solemnify2/REDKITE-F16-Panels/F16_LEFT_AUX_MISC/BiosHandler/DcsBiosParser.h

/*
  DcsBiosParser.h — DCS-BIOS binary frame parser for Teensy

  DCS-BIOS protocol:
    Sync: 0x55 0x55 0x55 0x55
    Then repeating: ADDR_LOW ADDR_HIGH COUNT_LOW COUNT_HIGH DATA[count]
    Frame end marker: address=0x5555, count=0x5555

  Only output addresses (LED control) are handled here.
  Switch input is handled via USB joystick (no DCS-BIOS write needed).
*/

#ifndef DCSBIOS_PARSER_H
#define DCSBIOS_PARSER_H

// ================================================================
//  DCS-BIOS F-16C Address Map
// ================================================================
// Source: DCS-BIOS F-16C_50.json
// These addresses may need verification against the actual JSON export.

// Address 0x447A: Nose gear (bit14), Left gear (bit15)
#define DCSBIOS_GEAR_NL_ADDR    0x447A
#define DCSBIOS_GEAR_NOSE_MASK  0x4000  // bit 14
#define DCSBIOS_GEAR_LEFT_MASK  0x8000  // bit 15

// Address 0x447C: Right gear (bit0)
#define DCSBIOS_GEAR_R_ADDR     0x447C
#define DCSBIOS_GEAR_RIGHT_MASK 0x0001  // bit 0

// Address 0x447C: Right gear (bit0), Gear Warning (bit1)
#define DCSBIOS_GEAR_WARN_MASK  0x0002  // bit 1 — LIGHT_GEAR_WARN (red)

// Address 0x447E: RWR/TWA + ADV indicator lights
#define DCSBIOS_TWA_ADDR          0x447E
#define DCSBIOS_ADV_ACTIVE_MASK   0x0004  // bit 2  — LIGHT_ACTIVE (green)
#define DCSBIOS_ADV_STBY_MASK     0x0008  // bit 3  — LIGHT_STBY (yellow)
#define DCSBIOS_TWA_SEARCH_MASK   0x0400  // bit 10 — LIGHT_RWR_SEARCH
#define DCSBIOS_TWA_ACT_MASK      0x0800  // bit 11 — LIGHT_RWR_ACTIVITY
#define DCSBIOS_TWA_POWER_MASK    0x1000  // bit 12 — LIGHT_RWR_ACT_POWER
#define DCSBIOS_TWA_LOW_MASK      0x2000  // bit 13 — LIGHT_RWR_ALT_LOW

// Address 0x4544: ECM indicator (bit14) — main ECM LED (separate from 32 SR LEDs)
#define DCSBIOS_ECM_ADDR        0x4544
#define DCSBIOS_ECM_MASK        0x4000  // bit 14

// Address 0x4484: LIGHT_INST_PNL — instrument panel backlight (0–65535)
#define DCSBIOS_INST_PNL_ADDR   0x4484

// ================================================================
//  Parser State Machine
// ================================================================

enum DcsBiosState {
  DCS_SYNC_1,
  DCS_SYNC_2,
  DCS_SYNC_3,
  DCS_SYNC_4,
  DCS_ADDR_LOW,
  DCS_ADDR_HIGH,
  DCS_COUNT_LOW,
  DCS_COUNT_HIGH,
  DCS_DATA
};

static DcsBiosState dcsBiosState = DCS_SYNC_1;
static uint16_t     dcsBiosAddr  = 0;
static uint16_t     dcsBiosCount = 0;
static uint16_t     dcsBiosSkip  = 0;
static uint8_t      dcsBiosDataBuf[2];
static bool         dcsBiosCapture = false;  // true if current chunk overlaps an address we care about
static uint8_t      dcsBiosSyncRun = 0;      // consecutive 0x55 bytes seen in DATA state (resync detector)
static uint32_t     dcsBiosLastByte = 0;     // millis() of last byte received (intra-frame timeout)

// ================================================================
//  Address Interest Check
// ================================================================

// Returns true if we need to process data for this 2-byte aligned address
static bool dcsBiosIsInteresting(uint16_t addr) {
  return (addr == DCSBIOS_GEAR_NL_ADDR || addr == DCSBIOS_GEAR_R_ADDR ||
          addr == DCSBIOS_TWA_ADDR || addr == DCSBIOS_ECM_ADDR ||
          addr == DCSBIOS_INST_PNL_ADDR);
}

// Returns true if the chunk [addr, addr+count) overlaps any interesting address
static bool dcsBiosChunkIsInteresting(uint16_t addr, uint16_t count) {
  uint16_t end = addr + count;
  return (DCSBIOS_GEAR_NL_ADDR    >= addr && DCSBIOS_GEAR_NL_ADDR    < end) ||
         (DCSBIOS_GEAR_R_ADDR     >= addr && DCSBIOS_GEAR_R_ADDR     < end) ||
         (DCSBIOS_TWA_ADDR        >= addr && DCSBIOS_TWA_ADDR        < end) ||
         (DCSBIOS_ECM_ADDR        >= addr && DCSBIOS_ECM_ADDR        < end) ||
         (DCSBIOS_INST_PNL_ADDR   >= addr && DCSBIOS_INST_PNL_ADDR   < end);
}

// ================================================================
//  Update Callback — called when a watched address has new data
// ================================================================

// Forward-declared LED array and indices from main .ino
// (LedIdx enum and leds[] are defined in the main sketch)
static void dcsBiosOnUpdate(uint16_t addr, uint16_t value) {
  if (addr == DCSBIOS_GEAR_NL_ADDR) {
    writeLed(LI_NOSE_GEAR, (value & DCSBIOS_GEAR_NOSE_MASK));
    writeLed(LI_LEFT_GEAR, (value & DCSBIOS_GEAR_LEFT_MASK));
  }
  else if (addr == DCSBIOS_GEAR_R_ADDR) {
    writeLed(LI_RIGHT_GEAR, (value & DCSBIOS_GEAR_RIGHT_MASK));
    writeLed(LI_GEAR_WARN, (value & DCSBIOS_GEAR_WARN_MASK));
  }
  else if (addr == DCSBIOS_TWA_ADDR) {
    //if (ALLOW_DEBUG) Serial.printf("[DCS] 0x447E = 0x%04X  ACT=%d STB=%d\n", value, !!(value & DCSBIOS_ADV_ACTIVE_MASK), !!(value & DCSBIOS_ADV_STBY_MASK));
    writeLed(LI_ADV_ACTIVE, (value & DCSBIOS_ADV_ACTIVE_MASK));
    writeLed(LI_ADV_STANDBY, (value & DCSBIOS_ADV_STBY_MASK));
    writeLed(LI_TWA_POWER, (value & DCSBIOS_TWA_POWER_MASK));
    writeLed(LI_TWA_LOW, (value & DCSBIOS_TWA_LOW_MASK));
    writeLed(LI_TWA_SEARCH, (value & DCSBIOS_TWA_SEARCH_MASK));
    writeLed(LI_TWA_ACT, (value & DCSBIOS_TWA_ACT_MASK));
  }
  else if (addr == DCSBIOS_ECM_ADDR) {
    writeLed(LI_ECM, (value & DCSBIOS_ECM_MASK));
  }
  else if (addr == DCSBIOS_INST_PNL_ADDR) {
    // Instrument panel backlight: PWM dimming (0~65535 → 0~255)
    setBacklightBrightness(value >> 8);
  }
}

// ================================================================
//  Reset Parser State
// ================================================================

void dcsBiosReset() {
  dcsBiosState   = DCS_SYNC_1;
  dcsBiosAddr    = 0;
  dcsBiosCount   = 0;
  dcsBiosSkip    = 0;
  dcsBiosCapture = false;
  dcsBiosSyncRun = 0;
  dcsBiosLastByte = 0;
}

// Intra-frame timeout check — call from loop() before processing bytes.
// If parser is mid-frame and no byte arrived for too long, force resync.
#define DCS_INTRA_FRAME_TIMEOUT_MS  200

void dcsBiosCheckTimeout() {
  if (dcsBiosState > DCS_SYNC_4 && dcsBiosLastByte != 0) {
    if (millis() - dcsBiosLastByte > DCS_INTRA_FRAME_TIMEOUT_MS) {
      //if (ALLOW_DEBUG) Serial.println("[DCS] Intra-frame timeout, resync");
      dcsBiosState = DCS_SYNC_1;
      dcsBiosSyncRun = 0;
    }
  }
}

// ================================================================
//  Process One Byte
// ================================================================

void processDcsBiosByte(uint8_t b) {
  dcsBiosLastByte = millis();

  // --- Resync detector: track consecutive 0x55 in non-sync states ---
  // If we see 4+ consecutive 0x55 while parsing data, we've hit a new frame sync.
  if (dcsBiosState > DCS_SYNC_4) {
    if (b == 0x55) {
      dcsBiosSyncRun++;
      if (dcsBiosSyncRun >= 4) {
        // New sync found mid-parse — force resync
        //if (ALLOW_DEBUG) Serial.println("[DCS] Resync: found 0x55x4 in data stream");
        dcsBiosState = DCS_ADDR_LOW;
        dcsBiosSyncRun = 0;
        return;
      }
    } else {
      dcsBiosSyncRun = 0;
    }
  }

  switch (dcsBiosState) {
    case DCS_SYNC_1:
      if (b == 0x55) dcsBiosState = DCS_SYNC_2;
      break;
    case DCS_SYNC_2:
      dcsBiosState = (b == 0x55) ? DCS_SYNC_3 : DCS_SYNC_1;
      break;
    case DCS_SYNC_3:
      dcsBiosState = (b == 0x55) ? DCS_SYNC_4 : DCS_SYNC_1;
      break;
    case DCS_SYNC_4:
      dcsBiosState = (b == 0x55) ? DCS_ADDR_LOW : DCS_SYNC_1;
      break;

    case DCS_ADDR_LOW:
      dcsBiosAddr = b;
      dcsBiosState = DCS_ADDR_HIGH;
      break;
    case DCS_ADDR_HIGH:
      dcsBiosAddr |= (uint16_t)b << 8;

      // Address sanity check: DCS-BIOS addresses are even and within export range.
      // Allow 0x5555 (frame end marker) and typical F-16 range 0x0000–0x8000.
      if ((dcsBiosAddr & 1) && dcsBiosAddr != 0x5555) {
        // Odd address (except end marker) = desync
        //if (ALLOW_DEBUG) Serial.printf("[DCS] Bad addr 0x%04X, resync\n", dcsBiosAddr);
        dcsBiosState = DCS_SYNC_1;
        break;
      }
      dcsBiosState = DCS_COUNT_LOW;
      break;
    case DCS_COUNT_LOW:
      dcsBiosCount = b;
      dcsBiosState = DCS_COUNT_HIGH;
      break;
    case DCS_COUNT_HIGH:
      dcsBiosCount |= (uint16_t)b << 8;

      // Frame end marker
      if (dcsBiosAddr == 0x5555 && dcsBiosCount == 0x5555) {
        dcsBiosState = DCS_SYNC_1;
        break;
      }

      // Count sanity check: must be even and reasonable (DCS-BIOS chunks are small)
      if ((dcsBiosCount & 1) || dcsBiosCount == 0 || dcsBiosCount > 1024) {
        //if (ALLOW_DEBUG) Serial.printf("[DCS] Bad count %u @ 0x%04X, resync\n", dcsBiosCount, dcsBiosAddr);
        dcsBiosState = DCS_SYNC_1;
        break;
      }

      dcsBiosCapture = dcsBiosChunkIsInteresting(dcsBiosAddr, dcsBiosCount);
      dcsBiosSkip    = 0;
      dcsBiosState   = DCS_DATA;
      break;

    case DCS_DATA:
      if (dcsBiosCapture) {
        // Accumulate bytes in pairs, processing each 2-byte word
        if ((dcsBiosSkip & 1) == 0) {
          dcsBiosDataBuf[0] = b;  // low byte
        } else {
          dcsBiosDataBuf[1] = b;  // high byte — word complete
          uint16_t wordAddr = dcsBiosAddr + (dcsBiosSkip & ~1u);
          if (dcsBiosIsInteresting(wordAddr)) {
            uint16_t value = dcsBiosDataBuf[0] | ((uint16_t)dcsBiosDataBuf[1] << 8);
            dcsBiosOnUpdate(wordAddr, value);
          }
        }
      }
      dcsBiosSkip++;

      if (dcsBiosSkip >= dcsBiosCount) {
        dcsBiosState = DCS_ADDR_LOW;  // Next chunk
      }
      break;
  }
}

#endif // DCSBIOS_PARSER_H
