solemnify2/REDKITE-F16-Panels/REDKITE_F16_LEFT_AUX_MISC/name.c

#include "usb_names.h"

struct usb_string_descriptor_struct usb_string_product_name = {
  2 + 25 * 2,  // 2 + (글자수 * 2)
  3,
  {'R','E','D','K','I','T','E',' ','F','1','6',' ','L','E','F','T',' ','A','U','X',' ','M','I','S','C'}
};
