solemnify2/REDKITE-F16-Panels/tools/bmsbios_bridge.py

#!/usr/bin/env python3
"""
BMS-BIOS Bridge (통합) — Falcon BMS Shared Memory -> 여러 Teensy Serial

통합 프레임 포맷 (모든 디바이스 동일):
  sync(2) + ledBits(4) + srData(4) + checksum(1) = 11 bytes
  각 디바이스는 자신에게 필요한 필드만 사용하고 나머지는 무시합니다.

사용법:
  python bmsbios_bridge.py                              (자동 감지)
  python bmsbios_bridge.py COM3:AUX COM4:CONSOLE        (수동 지정)
  python bmsbios_bridge.py --hz 20 --debug
"""

import sys
import time
import struct
import argparse
import mmap
import ctypes

# ================================================================
#  Falcon BMS Shared Memory
# ================================================================

SHM_NAME  = "FalconSharedMemoryArea"
SHM_SIZE  = 1024
SHM2_NAME = "FalconSharedMemoryArea2"
SHM2_SIZE = 1200

OFF_LIGHTBITS  = 108
OFF_LIGHTBITS2 = 124
OFF_LIGHTBITS3 = 128
OFF_FD2_INSTRLIGHT = 1104
OFF_FD2_ECMBITS    = 1180   # unsigned int ecmBits[5] (VERSION 19)
OFF_FD2_ECMOPER    = 1200   # unsigned char ecmOper   (VERSION 19)
OFF_FD2_UHF_PRESET = 48     # int uhf_panel_preset    (BUP UHF 채널)
OFF_FD2_UHF_FREQ   = 52     # int uhf_panel_frequency (BUP UHF 주파수)

# --- LightBits (offset 108) ---
LB_ADV_STANDBY      = 0x80000000  # bit 31

# --- LightBits2 (offset 124) ---
LB2_EWS_GO          = 0x00000040  # bit 6  - CMDS GO (정상 동작)
LB2_EWS_NOGO        = 0x00000080  # bit 7  - CMDS NO GO (고장)
LB2_EWS_RDY         = 0x00000200  # bit 9  - CMDS DISPENSE RDY
LB2_AUX_SRCH        = 0x00001000  # bit 12
LB2_AUX_ACT         = 0x00002000  # bit 13
LB2_AUX_LOW         = 0x00004000  # bit 14
LB2_AUX_PWR         = 0x00008000  # bit 15
LB2_ECM_PWR         = 0x00010000  # bit 16
LB2_EPU_ON          = 0x00100000  # bit 20 - EPU panel; run light
LB2_JFS_ON          = 0x00200000  # bit 21 - Eng Jet Start panel; run light
LB2_ADV_ACTIVE      = 0x20000000  # bit 29
LB_GEARHANDLE       = 0x40000000  # bit 30

# --- LightBits3 (offset 128, from FlightData.h) ---
LB3_FLCS_PMG        = 0x00000001  # bit 0  — ELEC panel
LB3_MAIN_GEN        = 0x00000002  # bit 1
LB3_STBY_GEN        = 0x00000004  # bit 2
LB3_EPU_GEN         = 0x00000008  # bit 3
LB3_EPU_PMG         = 0x00000010  # bit 4
LB3_TO_FLCS         = 0x00000020  # bit 5
LB3_FLCS_RLY        = 0x00000040  # bit 6
LB3_BAT_FAIL        = 0x00000080  # bit 7
LB3_HYDRAZINE       = 0x00000100  # bit 8  - EPU HYDRAZN
LB3_AIR             = 0x00000200  # bit 9  - EPU AIR
LB3_NOSE_GEAR_DN    = 0x00010000  # bit 16
LB3_LEFT_GEAR_DN    = 0x00020000  # bit 17
LB3_RIGHT_GEAR_DN   = 0x00040000  # bit 18

# ================================================================
#  Device Profiles
# ================================================================

# LEFT_AUX: 11 direct GPIO LEDs + backlight (bit 16)
AUX_LED_MAP = [
    (0,  OFF_LIGHTBITS3, LB3_NOSE_GEAR_DN),  # NOSE GEAR
    (1,  OFF_LIGHTBITS3, LB3_LEFT_GEAR_DN),  # LEFT GEAR
    (2,  OFF_LIGHTBITS3, LB3_RIGHT_GEAR_DN), # RIGHT GEAR
    (3,  OFF_LIGHTBITS2, LB_GEARHANDLE),     # GEAR WARN
    (4,  OFF_LIGHTBITS2, LB2_AUX_PWR),       # TWA POWER
    (5,  OFF_LIGHTBITS2, LB2_AUX_LOW),       # TWA LOW
    (6,  OFF_LIGHTBITS2, LB2_AUX_SRCH),      # TWA SEARCH
    (7,  OFF_LIGHTBITS2, LB2_AUX_ACT),       # TWA ACT
    (8,  OFF_LIGHTBITS2, LB2_ECM_PWR),       # ECM
    (9,  OFF_LIGHTBITS2, LB2_ADV_ACTIVE),    # ADV ACTIVE
    (10, OFF_LIGHTBITS,  LB_ADV_STANDBY),    # ADV STANDBY
    # CMDS EWS 램프 — 신호 3개가 LED 6개를 구동 (같은 비트를 여러 LED 에 중복 매핑)
    (11, OFF_LIGHTBITS2, LB2_EWS_GO),        # CMDS GO      LED x1
    (12, OFF_LIGHTBITS2, LB2_EWS_NOGO),      # CMDS NO GO 1
    (13, OFF_LIGHTBITS2, LB2_EWS_NOGO),      # CMDS NO GO 2
    (14, OFF_LIGHTBITS2, LB2_EWS_RDY),       # CMDS RDY 1
    (15, OFF_LIGHTBITS2, LB2_EWS_RDY),       # CMDS RDY 2
    (16, OFF_LIGHTBITS2, LB2_EWS_RDY),       # CMDS RDY 3
]

# LEFT_CONSOLE: 12 LEDs - ELEC 8 (bit 0-7) + EPU 3 (bit 8-10) + ENGINE RUN (bit 11)
# 마스크 출처: Falcon BMS 4.38 Tools/SharedMem/FlightData.h
CONSOLE_LED_MAP = [
    (0,  OFF_LIGHTBITS3, LB3_FLCS_PMG),     # FLCS PMG
    (1,  OFF_LIGHTBITS3, LB3_MAIN_GEN),     # MAIN GEN
    (2,  OFF_LIGHTBITS3, LB3_STBY_GEN),     # STBY GEN
    (3,  OFF_LIGHTBITS3, LB3_EPU_GEN),      # EPU GEN
    (4,  OFF_LIGHTBITS3, LB3_EPU_PMG),      # EPU PMG
    (5,  OFF_LIGHTBITS3, LB3_TO_FLCS),      # BATT TO FLCS
    (6,  OFF_LIGHTBITS3, LB3_FLCS_RLY),     # FLCS RLY
    (7,  OFF_LIGHTBITS3, LB3_BAT_FAIL),     # BATT FAIL
    # --- EPU 패널 3 ---
    (8,  OFF_LIGHTBITS3, LB3_HYDRAZINE),    # EPU HYDRAZN
    (9,  OFF_LIGHTBITS3, LB3_AIR),          # EPU AIR
    (10, OFF_LIGHTBITS2, LB2_EPU_ON),       # EPU RUN
    # --- ENGINE START 패널 1 ---
    (11, OFF_LIGHTBITS2, LB2_JFS_ON),       # JFS RUN
]

# --- EcmBits enum (mutually exclusive states per program) ---
ECM_UNPRESSED_NO_LIT  = 0x01
ECM_UNPRESSED_ALL_LIT = 0x02
ECM_PRESSED_NO_LIT    = 0x04
ECM_PRESSED_STANDBY   = 0x08
ECM_PRESSED_ACTIVE    = 0x10
ECM_PRESSED_TRANSMIT  = 0x20
ECM_PRESSED_FAIL      = 0x40
ECM_PRESSED_ALL_LIT   = 0x80

MAX_ECM_PROGRAMS = 5

SYNC = b'\xAA\xBB'

# ================================================================
#  Frame Builder
# ================================================================

ZERO4 = bytes(4)


def build_frame(led_bits: int, sr_data: bytes = ZERO4, uhf=(0, 0)) -> bytes:
    """통합 16바이트 프레임
      sync(2) + ledBits(4) + srData(4) + uhfFreq(4) + uhfPreset(1) + checksum(1)

    모든 Teensy 장치가 같은 프레임을 받고, 필요 없는 필드는 무시합니다.
      AUX     : ledBits 만 사용
      CONSOLE : 전부 사용 (srData = ECM 시프트레지스터, uhf* = 7세그 디스플레이)"""
    khz, preset = uhf
    payload = (struct.pack('<I', led_bits) + sr_data
               + struct.pack('<IB', khz & 0xFFFFFFFF, preset & 0xFF))
    checksum = 0
    for b in payload:
        checksum ^= b
    return SYNC + payload + bytes([checksum])


def read_uhf(shm2):
    """BUP UHF 주파수(kHz)와 프리셋 채널을 FlightData2 에서 읽습니다.

    주파수 단위가 BMS 버전에 따라 다를 수 있어, 100000~999999 kHz 를
    벗어나면 0 으로 보내 Teensy 가 대시를 표시하게 합니다."""
    if shm2 is None:
        return (0, 0)
    try:
        preset = read_int32(shm2, OFF_FD2_UHF_PRESET)
        freq   = read_int32(shm2, OFF_FD2_UHF_FREQ)
    except Exception:
        return (0, 0)
    if not (100000 <= freq <= 999999):
        freq = 0
    if not (0 <= preset <= 99):
        preset = 0
    return (freq, preset)

# ================================================================
#  Shared Memory Reader
# ================================================================

def open_shm(name, size):
    try:
        kernel32 = ctypes.windll.kernel32
        handle = kernel32.OpenFileMappingW(0x0004, False, name)
        if not handle:
            return None
        kernel32.CloseHandle(handle)
        return mmap.mmap(-1, size, tagname=name, access=mmap.ACCESS_READ)
    except Exception:
        return None


def read_int32(shm, offset):
    shm.seek(offset)
    return struct.unpack('<i', shm.read(4))[0]


def read_byte(shm, offset):
    shm.seek(offset)
    return struct.unpack('B', shm.read(1))[0]


def compute_led_bits(led_map, lbits):
    """LED 매핑 테이블로부터 ledBits 계산"""
    led_bits = 0
    for idx, offset, mask in led_map:
        if lbits[offset] & mask:
            led_bits |= (1 << idx)
    return led_bits


def ecm_bits_to_saft(ecm_state):
    """EcmBits 상태를 S/A/F/T LED 4비트로 변환.
    Returns (s, a, f, t) as bools.
    S=Standby, A=Active, F=Fail, T=Transmit
    ALL_LIT = all four on.
    """
    if ecm_state == ECM_PRESSED_STANDBY:
        return (True, False, False, False)
    elif ecm_state == ECM_PRESSED_ACTIVE:
        return (False, True, False, False)
    elif ecm_state == ECM_PRESSED_FAIL:
        return (False, False, True, False)
    elif ecm_state == ECM_PRESSED_TRANSMIT:
        return (False, False, False, True)
    elif ecm_state in (ECM_UNPRESSED_ALL_LIT, ECM_PRESSED_ALL_LIT):
        return (True, True, True, True)
    else:
        return (False, False, False, False)


def compute_ecm_sr_data(shm2):
    """FlightData2의 ecmBits[5]로부터 ECM SR 32비트 데이터 생성.
    SR layout: [ECM1_S,A,F,T, ECM2_S,A,F,T, ..., ECM5_S,A,F,T, ECM6_S,A,F,T, FRM_S,A,F,T, SPL_S,A,F,T]
    ECM programs 1-5 map to ecmBits[0-4]. ECM6/FRM/SPL are not in shared memory (always off).
    """
    sr_bits = 0
    for pgm in range(MAX_ECM_PROGRAMS):
        shm2.seek(OFF_FD2_ECMBITS + pgm * 4)
        ecm_val = struct.unpack('<I', shm2.read(4))[0]
        s, a, f, t = ecm_bits_to_saft(ecm_val)
        base = pgm * 4
        if s: sr_bits |= (1 << (base + 0))
        if a: sr_bits |= (1 << (base + 1))
        if f: sr_bits |= (1 << (base + 2))
        if t: sr_bits |= (1 << (base + 3))
    # ECM6(20-23), FRM(24-27), SPL(28-31) — no shared memory source, stay 0
    return struct.pack('<I', sr_bits)

# ================================================================
#  Device Profiles — per-device LED map + frame builder
# ================================================================

DEVICE_PROFILES = {
    'AUX': {
        'led_map': AUX_LED_MAP,
        'has_backlight': True,
        'has_ecm': False,
    },
    'CONSOLE': {
        'led_map': CONSOLE_LED_MAP,
        # 좌측 콘솔 확장(EPU/AUDIO/UHF/ENGINE/MPO)에 백라이트 추가됨
        'has_backlight': True,
        'has_ecm': True,
    },
}

# ================================================================
#  Device Class
# ================================================================

DIM_PWM_DEFAULT = 255   # DIM 초기값 (BRT 미수신 시 최대 밝기)
DIM_PWM_LOWERED = 50    # BRT 수신 후 DIM 밝기
BRT_PWM         = 255

class Device:
    def __init__(self, port, dev_type, ser):
        self.port = port
        self.dev_type = dev_type
        self.ser = ser
        self.prev_frame = None
        self.profile = DEVICE_PROFILES[dev_type]
        self.brt_seen = False   # instrLight=2 수신 여부

    def build_and_send(self, lbits, shm2):
        led_bits = compute_led_bits(self.profile['led_map'], lbits)

        if self.profile['has_backlight'] and shm2 is not None:
            instr = read_byte(shm2, OFF_FD2_INSTRLIGHT)
            if instr >= 2 and not self.brt_seen:
                self.brt_seen = True
                print(f"[{self.port}] instrLight=2(BRT) 감지 — DIM 밝기 {DIM_PWM_LOWERED}로 전환")
            # 0=OFF, 1=DIM, 2+=BRT
            if instr == 0:
                brightness = 0
            elif instr >= 2:
                brightness = BRT_PWM
            else:  # instr == 1 (DIM)
                brightness = DIM_PWM_LOWERED if self.brt_seen else DIM_PWM_DEFAULT
            led_bits |= (brightness << 16)

        sr_data = compute_ecm_sr_data(shm2) if self.profile['has_ecm'] and shm2 else ZERO4
        uhf = read_uhf(shm2)        # 통합 프레임 — AUX 는 이 필드를 무시합니다
        frame = build_frame(led_bits, sr_data, uhf)

        if frame != self.prev_frame:
            try:
                self.ser.write(frame)
                self.prev_frame = frame
            except Exception:
                pass

    def heartbeat(self):
        """Send current frame as heartbeat even if unchanged."""
        if self.prev_frame:
            try:
                self.ser.write(self.prev_frame)
            except Exception:
                pass


# ================================================================
#  Port Argument Parser
# ================================================================

def parse_port_arg(arg):
    """Parse 'COM3:AUX' or 'COM3' format. Auto-detect type if not specified."""
    if ':' in arg:
        port, dtype = arg.split(':', 1)
        dtype = dtype.upper()
        if dtype not in ('AUX', 'CONSOLE'):
            print(f"알 수 없는 디바이스 타입: {dtype} (AUX 또는 CONSOLE)")
            sys.exit(1)
        return port, dtype
    return arg, None


def detect_device_type(port):
    """VID/PID 기반 디바이스 타입 추정"""
    import serial.tools.list_ports
    for p in serial.tools.list_ports.comports():
        if p.device == port and p.vid == TEENSY_VID:
            entry = PID_DEVICES.get(p.pid)
            if entry:
                return entry[1]
    return None


TEENSY_VID = 0x16C0

# PID → (display name, device type)
# device type: 'AUX' or 'CONSOLE' (used for frame format selection)
# 새 Teensy 추가 시 여기에 한 줄 추가
PID_DEVICES = {
    0x0487: ("F16 LEFT AUX MISC",          "AUX"),      # default Teensy PID
    0x0489: ("F16 LEFT AUX MISC",          "AUX"),
    0x048E: ("F16 LEFT CONSOLE",           "CONSOLE"),
}


def find_teensy_ports():
    """VID 기반 Teensy COM 포트 자동 감지 + PID로 디바이스 타입 판별.
    Returns (port_args, descriptions): port_args is list of 'COMx:TYPE' or 'COMx', descriptions for display."""
    import serial.tools.list_ports
    ports = serial.tools.list_ports.comports()
    port_args = []
    descriptions = []
    for p in ports:
        if p.vid == TEENSY_VID:
            entry = PID_DEVICES.get(p.pid)
            if entry:
                name, dtype = entry
                port_args.append(f"{p.device}:{dtype}")
                descriptions.append(f"  {p.device}: {name} [{dtype}]")
            else:
                port_args.append(p.device)
                descriptions.append(f"  {p.device}: Unknown (PID:0x{p.pid:04X})")
    return port_args, descriptions

# ================================================================
#  Main
# ================================================================

def main():
    parser = argparse.ArgumentParser(description='BMS-BIOS Bridge (통합)')
    parser.add_argument('ports', nargs='*',
                        help='COM ports: COM3:AUX COM4:CONSOLE (or just COM3 COM4 for auto-detect)')
    parser.add_argument('--baud', type=int, default=1000000)
    parser.add_argument('--hz', type=int, default=20)
    parser.add_argument('--debug', action='store_true')
    args = parser.parse_args()

    import serial as pyserial

    # 포트 결정
    port_args = args.ports
    if not port_args:
        auto, descs = find_teensy_ports()
        if auto:
            port_args = auto
        else:
            import serial.tools.list_ports
            all_ports = serial.tools.list_ports.comports()
            print("Teensy를 자동 감지하지 못했습니다.")
            if all_ports:
                print("사용 가능한 COM 포트:")
                for p in all_ports:
                    vid_str = f"VID:0x{p.vid:04X}" if p.vid else "VID:N/A"
                    pid_str = f"PID:0x{p.pid:04X}" if p.pid else "PID:N/A"
                    print(f"  {p.device}: {p.description} [{vid_str} {pid_str}]")
            print("포트를 인자로 지정하세요. 예: python bmsbios_bridge.py COM3:AUX COM4:CONSOLE")
            sys.exit(1)

    # 디바이스 생성
    devices = []
    failed = False
    for pa in port_args:
        port, dtype = parse_port_arg(pa)
        if dtype is None:
            dtype = detect_device_type(port)
            if dtype is None:
                print(f"  {port}: 디바이스 타입 자동 감지 실패. COM:TYPE 형식으로 지정하세요 (예: {port}:AUX)")
                continue
        try:
            s = pyserial.Serial(port, args.baud, timeout=0)
            dev = Device(port, dtype, s)
            devices.append(dev)
            name = next((n for pid, (n, t) in PID_DEVICES.items() if t == dtype), dtype)
            print(f"  {port}: {name} [{dtype}]")
        except pyserial.SerialException as e:
            print(f"  {port}: 열기 실패 — {e}")
            failed = True

    if failed:
        import serial.tools.list_ports
        all_ports = serial.tools.list_ports.comports()
        if all_ports:
            print("현재 검색되는 COM 포트:")
            for p in all_ports:
                print(f"  {p.device}: {p.description}")
        else:
            print("시스템에 COM 포트가 없습니다.")

    if not devices:
        sys.exit(1)

    print(f"\n[BMS-BIOS] Update rate: {args.hz} Hz")
    print(f"[BMS-BIOS] Waiting for Falcon BMS shared memory...")

    interval = 1.0 / args.hz
    shm = None
    shm2 = None

    try:
        while True:

            if shm is None:
                shm = open_shm(SHM_NAME, SHM_SIZE)
                if shm is not None:
                    print("[BMS-BIOS] BMS shared memory connected!")
            if shm2 is None:
                shm2 = open_shm(SHM2_NAME, SHM2_SIZE)
                if shm2 is not None:
                    print("[BMS-BIOS] FlightData2 connected")

            if shm is not None:
                try:
                    lb  = read_int32(shm, OFF_LIGHTBITS)
                    lb2 = read_int32(shm, OFF_LIGHTBITS2)
                    lb3 = read_int32(shm, OFF_LIGHTBITS3)
                    lbits = {OFF_LIGHTBITS: lb, OFF_LIGHTBITS2: lb2, OFF_LIGHTBITS3: lb3}

                    if args.debug:
                        instr_dbg = read_byte(shm2, OFF_FD2_INSTRLIGHT) if shm2 else -1
                        print(f"  LB=0x{lb:08X}  LB2=0x{lb2:08X}  LB3=0x{lb3:08X}  instrLight={instr_dbg}")

                    for dev in devices:
                        dev.build_and_send(lbits, shm2)

                    # Periodic heartbeat
                    if int(time.time() * args.hz) % args.hz == 0:
                        for dev in devices:
                            dev.heartbeat()


                except Exception as e:
                    print(f"\n[BMS-BIOS] SHM read error: {e}, reconnecting...")
                    try: shm.close()
                    except: pass
                    try:
                        if shm2: shm2.close()
                    except: pass
                    shm = None
                    shm2 = None
                    for dev in devices:
                        dev.prev_frame = None

            time.sleep(interval)

    except KeyboardInterrupt:
        print("\n[BMS-BIOS] Stopped.")
    finally:
        for dev in devices:
            dev.ser.close()
        if shm: shm.close()
        if shm2: shm2.close()


if __name__ == '__main__':
    main()
